tvelliott/SDR_at86rf215/firmware/channel_filter.c

//MIT License
//
//Copyright (c) 2018 tvelliott
//
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




#include <math.h>
#include <float.h>
#include <complex.h>
#include "arm_math.h"
#include "channel_filter.h"


//decimation

static float32_t fir_dec_state_f32_I_8[NSAMPLES + 128 - 1];
static float32_t fir_dec_state_f32_Q_8[NSAMPLES + 128 - 1];
static arm_fir_decimate_instance_f32 Si_dec_8;
static arm_fir_decimate_instance_f32 Sq_dec_8;

static float32_t fir_dec_state_f32_I_32[NSAMPLES + 128 - 1];
static float32_t fir_dec_state_f32_Q_32[NSAMPLES + 128 - 1];
static arm_fir_decimate_instance_f32 Si_dec_32;
static arm_fir_decimate_instance_f32 Sq_dec_32;

static float32_t dc_state_f32_I[NSAMPLES + 134 - 1];
static float32_t dc_state_f32_Q[NSAMPLES + 134 - 1];
static arm_fir_instance_f32 dc_i;
static arm_fir_instance_f32 dc_q;

static float32_t fir_dec_state_f32_i_stage1[NSAMPLES + 128 - 1];
static float32_t fir_dec_state_f32_q_stage1[NSAMPLES + 128 - 1];
static arm_fir_decimate_instance_f32 fir_i_stage1;
static arm_fir_decimate_instance_f32 fir_q_stage1;

static float32_t fir_dec_state_f32_i_stage2[NSAMPLES + 128 - 1];
static float32_t fir_dec_state_f32_q_stage2[NSAMPLES + 128 - 1];
static arm_fir_decimate_instance_f32 fir_i_stage2;
static arm_fir_decimate_instance_f32 fir_q_stage2;

float32_t iout[256];
float32_t qout[256];

float dc_removal_63[] = {
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
    , 0.00000, -0.00636, -0.00368, 0.00345, 0.00525, 0.00000, -0.00466, -0.00271, 0.00256, 0.00392, 0.00000, -0.00350, -0.00205, 0.00194, 0.00298, 0.00000
    , -0.00267, -0.00157, 0.00148, 0.00228, 0.00000, -0.00205, -0.00120, 0.00114, 0.00174, 0.00000, -0.00156, -0.00091, 0.00087, 0.00132, 0.00000, -0.00118
    , -0.00069, 0.00065, 0.00100, 0.00000, -0.00089, -0.00052, 0.00049, 0.00074, -0.00000, -0.00066, -0.00038, 0.00036, 0.00055, 0.00000, -0.00048, -0.00028
    , 0.00026, 0.00039, 0.00000, -0.00034, -0.00020, 0.00018, 0.00028, -0.00000, -0.00024, -0.00014, 0.00013, 0.00019, 0.00000, -0.00016, -0.00009, 0.00009
    , 0.00013, 0.00000, -0.00011, -0.00006, 0.00006, 0.00008, -0.00000, -0.00007, -0.00004, 0.00004, 0.00005, 0.00000, -0.00004, -0.00002, 0.00002, 0.00003
    , 0.00000, -0.00003, -0.00001, 0.00001, 0.00002, -0.00000, -0.00001, -0.00001, 0.00001, 0.00001, 0.00000, -0.00001, -0.00000, 0.00000, 0.00000, 0.00000
    , -0.00000, -0.00000, 0.00000, 0.00000, 0.00000, -0.00000, -0.00000, 0.00000, 0.00000, 0.00000, -0.00000, -0.00000, 0.00000, 0.00000, -0.00000
  };

int8_t init_dc_removal = 0;
int8_t init_fir_dec_8 = 0;
int8_t init_fir_dec_32 = 0;
int8_t init_fir_stage1 = 0;
int8_t init_fir_stage2 = 0;

static float32_t input_i[NSAMPLES];
static float32_t input_q[NSAMPLES];

/////////////////////////////////////////////////////
/////////////////////////////////////////////////////
void cf_fft_shift( float32_t *data, int len )
{
  float32_t tmp[2048];
  int i;
  if( len > 2048 ) len = 2048;

  for( i = 0; i < len / 2; i++ ) {
    tmp[i] = data[i + len / 2];
  }
  for( i = 0; i < len / 2; i++ ) {
    tmp[i + len / 2] = data[i];
  }
  for( i = 0; i < len; i++ ) {
    data[i] = tmp[i];
  }
}
//////////////////////////////////////////////////////////////////////////////////////////////////////
//////////////////////////////////////////////////////////////////////////////////////////////////////
void do_fircomp_dec2_stage1( float complex *in_data )
{
  int i;

  if( !init_fir_stage1 ) {
    arm_fir_decimate_init_f32( &fir_i_stage1, 128, 2, &fir_comp_filter[0], &fir_dec_state_f32_i_stage1[0], 256 );
    arm_fir_decimate_init_f32( &fir_q_stage1, 128, 2, &fir_comp_filter[0], &fir_dec_state_f32_q_stage1[0], 256 );
    init_fir_stage1 = 1;
  }

  for( i = 0; i < 256; i++ ) {
    input_i[i] = ( float32_t ) creal( in_data[i] );
    input_q[i] = ( float32_t ) cimag( in_data[i] );
  }

  arm_fir_decimate_f32( &fir_i_stage1, input_i, iout, 256 );
  arm_fir_decimate_f32( &fir_q_stage1, input_q, qout, 256 );

}
//////////////////////////////////////////////////////////////////////////////////////////////////////
//////////////////////////////////////////////////////////////////////////////////////////////////////
void do_fircomp_dec2_stage2( float complex *in_data )
{
  int i;

  if( !init_fir_stage2 ) {
    arm_fir_decimate_init_f32( &fir_i_stage2, 128, 2, &fir_comp_filter[0], &fir_dec_state_f32_i_stage2[0], 128 );
    arm_fir_decimate_init_f32( &fir_q_stage2, 128, 2, &fir_comp_filter[0], &fir_dec_state_f32_q_stage2[0], 128 );
    init_fir_stage2 = 1;
  }

  for( i = 0; i < 128; i++ ) {
    input_i[i] = ( float32_t ) creal( in_data[i] );
    input_q[i] = ( float32_t ) cimag( in_data[i] );
  }

  arm_fir_decimate_f32( &fir_i_stage2, input_i, iout, 128 );
  arm_fir_decimate_f32( &fir_q_stage2, input_q, qout, 128 );

}

//////////////////////////////////////////////////////////////////////////////////////////////////////
//////////////////////////////////////////////////////////////////////////////////////////////////////
void do_filter_decimate_8( float complex *iqdata )
{

  int i;

  if( !init_fir_dec_8 ) {
    arm_fir_decimate_init_f32( &Si_dec_8, 128, 8, &channel_filter[0], &fir_dec_state_f32_I_8[0], NSAMPLES );
    arm_fir_decimate_init_f32( &Sq_dec_8, 128, 8, &channel_filter[0], &fir_dec_state_f32_Q_8[0], NSAMPLES );
    init_fir_dec_8 = 1;
  }


  //I filtering

  for( i = 0; i < NSAMPLES; i++ ) {
    input_i[i] = ( float32_t ) creal( iqdata[i] );
    input_q[i] = ( float32_t ) cimag( iqdata[i] );
  }
  arm_fir_decimate_f32( &Si_dec_8, input_i, iout, NSAMPLES );
  arm_fir_decimate_f32( &Sq_dec_8, input_q, qout, NSAMPLES );

}
//////////////////////////////////////////////////////////////////////////////////////////////////////
//////////////////////////////////////////////////////////////////////////////////////////////////////
void do_filter_decimate_32( float complex *iqdata )
{

  int i;

  if( !init_fir_dec_32 ) {
    arm_fir_decimate_init_f32( &Si_dec_32, 128, 32, &channel_filter[0], &fir_dec_state_f32_I_32[0], NSAMPLES );
    arm_fir_decimate_init_f32( &Sq_dec_32, 128, 32, &channel_filter[0], &fir_dec_state_f32_Q_32[0], NSAMPLES );
    init_fir_dec_32 = 1;
  }


  //I filtering

  for( i = 0; i < NSAMPLES; i++ ) {
    input_i[i] = ( float32_t ) creal( iqdata[i] );
    input_q[i] = ( float32_t ) cimag( iqdata[i] );
  }
  arm_fir_decimate_f32( &Si_dec_32, input_i, iout, NSAMPLES );
  arm_fir_decimate_f32( &Sq_dec_32, input_q, qout, NSAMPLES );

}
//static float32_t dc_state_f32_I[NSAMPLES + 128 -1];
//static float32_t dc_state_f32_Q[NSAMPLES + 128 -1];
//static arm_fir_dc_instance_f32 dc_i;
//static arm_fir_dc_instance_f32 dc_q;
//////////////////////////////////////////////////////////////////////////////////////////////////////
//////////////////////////////////////////////////////////////////////////////////////////////////////
float dc_removal( float complex *iqdata, float *ioff, float *qoff )
{

  int i;

  if( !init_dc_removal ) {
    arm_fir_init_f32( &dc_i, 63, &dc_removal_63[0], &dc_state_f32_I[0], NSAMPLES );
    arm_fir_init_f32( &dc_q, 63, &dc_removal_63[0], &dc_state_f32_Q[0], NSAMPLES );
    init_dc_removal = 1;
  }


  for( i = 0; i < NSAMPLES; i++ ) {
    input_i[i] = ( float32_t ) creal( iqdata[i] );
    input_q[i] = ( float32_t ) cimag( iqdata[i] );
  }
  arm_fir_f32( &dc_i, input_i, iout, NSAMPLES );
  arm_fir_f32( &dc_q, input_q, qout, NSAMPLES );

  float f1 = 0.0f;
  float f2 = 0.0f;
  for( i = 0; i < NSAMPLES; i++ ) {
    f1 += iout[i];
    f2 += qout[i];
  }
  *ioff = f1;
  *qoff = f2;

}
