tvelliott/SDR_at86rf215/firmware/fpga_image.h

//filename: fpga/src/fpga_top.bin
//input file length: 135100
//compressed len: 31387
const uint8_t rle_compressed_fpga_image[] = {
  0xff, 0x00, 0x00, 0x00, 0xff, 0x7e, 0xaa, 0x99, 0x7e, 0x51, 0x00, 0x01, 0x05, 0x92, 0x00, 0x20, 0x62, 0x03, 0x67, 0x72, 0x01, 0x10, 0x82, 0x00, 0x00, 0x00, 0x11, 0x00, 0x01, 0x01, 0x00, 0x00, 0x00,
  0x15, 0x80, 0x00, 0x00, 0x03, 0x02, 0x00, 0x00, 0x04, 0x08, 0x00, 0x00, 0x17, 0x80, 0x00, 0x00, 0x03, 0x02, 0x00, 0x00, 0x04, 0x08, 0x00, 0x00, 0x04, 0x20, 0x00, 0x00, 0x05, 0x07, 0x00, 0x00,
  0x28, 0x0d, 0x00, 0x00, 0x40, 0x80, 0x00, 0x00, 0x0a, 0xd0, 0x00, 0x00, 0x0b, 0x04, 0x00, 0x00, 0x0b, 0x40, 0x00, 0x00, 0x03, 0x01, 0x00, 0x00, 0x04, 0x04, 0x00, 0x00, 0x17, 0x40, 0x00, 0x00,
  0x03, 0x01, 0x00, 0x00, 0x04, 0x04, 0x00, 0x00, 0x04, 0x10, 0x00, 0x00, 0x11, 0x04, 0x00, 0x00, 0x6e, 0x20, 0x00, 0x00, 0x17, 0x80, 0x00, 0x00, 0x00, 0x03, 0x00, 0x00, 0x00, 0x02, 0x00, 0x00,
  0x01, 0x08, 0x00, 0x00, 0x00, 0x08, 0x00, 0x00, 0x17, 0x80, 0x00, 0x00, 0x00, 0x01, 0x00, 0x00, 0x00, 0x02, 0x00, 0x00, 0x01, 0x04, 0x00, 0x00, 0x00, 0x08, 0x00, 0x00, 0x01, 0x10, 0x00, 0x00,
  0x00, 0x20, 0x00, 0x00, 0x01, 0x40, 0x00, 0x00, 0x20, 0x40, 0x00, 0x00, 0x0b, 0x03, 0x00, 0x00, 0x04, 0x04, 0x00, 0x00, 0x04, 0x30, 0x00, 0x00, 0x16, 0x01, 0x00, 0x00, 0x04, 0x04, 0x00, 0x00,
  0x04, 0x10, 0x00, 0x00, 0x04, 0xc0, 0x00, 0x00, 0x33, 0x14, 0x00, 0x00, 0xc4, 0x10, 0x00, 0x00, 0x18, 0x20, 0x00, 0x00, 0x05, 0xe0, 0x00, 0x00, 0x10, 0x80, 0x00, 0x00, 0x03, 0x10, 0x00, 0x00,
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
  0x04, 0x00, 0x0c, 0xcc, 0x00, 0x20, 0x00, 0x50, 0x00, 0x23, 0x30, 0x00, 0x80, 0x00, 0x00, 0x01, 0x8c, 0xc0, 0x04, 0x00, 0x00, 0x3d, 0x3e, 0x00, 0x00, 0x02, 0x10, 0x00, 0x00, 0x00, 0xa0, 0x04,
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
};
