tvelliott/SDR_at86rf215/firmware/ext_tuner/main.h

/**
  ******************************************************************************
  * @file    main.h
  * @author  MCD Application Team
  * @version V1.0.0
  * @date    19-September-2011
  * @brief   Header for main.c module
  ******************************************************************************
  * @attention
  *
  * THE PRESENT FIRMWARE WHICH IS FOR GUIDANCE ONLY AIMS AT PROVIDING CUSTOMERS
  * WITH CODING INFORMATION REGARDING THEIR PRODUCTS IN ORDER FOR THEM TO SAVE
  * TIME. AS A RESULT, STMICROELECTRONICS SHALL NOT BE HELD LIABLE FOR ANY
  * DIRECT, INDIRECT OR CONSEQUENTIAL DAMAGES WITH RESPECT TO ANY CLAIMS ARISING
  * FROM THE CONTENT OF SUCH FIRMWARE AND/OR THE USE MADE BY CUSTOMERS OF THE
  * CODING INFORMATION CONTAINED HEREIN IN CONNECTION WITH THEIR PRODUCTS.
  *
  * <h2><center>&copy; COPYRIGHT 2011 STMicroelectronics</center></h2>
  ******************************************************************************
  */

/* Define to prevent recursive inclusion -------------------------------------*/
#ifndef __STM32F4_DISCOVERY_DEMO_H
#define __STM32F4_DISCOVERY_DEMO_H

/* Includes ------------------------------------------------------------------*/
#include "stm32f4_discovery.h"
#include <stdio.h>

void TimingDelay_Decrement(void);
void Delay(__IO uint32_t nTime);
void Fail_Handler(void);
#endif /* __STM32F4_DISCOVERY_DEMO_H */

/******************* (C) COPYRIGHT 2011 STMicroelectronics *****END OF FILE****/
