tvelliott/SDR_at86rf215/firmware/ext_tuner/syscalls_newlib.c

//MIT License
//
//Copyright (c) 2018 tvelliott
//
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

#include <sys/types.h>
#include <stdint.h>
#include <errno.h>


extern int32_t _heap;
static unsigned char *heap_ptr = NULL;
int errno;
int _errno;

//calling pow() function causes errors with newlib
//including <errno.h> didn't help
//newlib was complaining about __error not being defined
//no idea if this is right, but compiles
int32_t error = 0;
int * __errno( void )
{
  return &error;
}

//////////////////////////////////////////////////////////////
//  this is used by libc (newlib) when calling malloc / free
//  the heap area is defined in main.ld
//////////////////////////////////////////////////////////////
caddr_t _sbrk(int32_t incr)
{
  unsigned char *prev_heap;

  if(heap_ptr == NULL) {
    heap_ptr = (unsigned char *)&_heap;
  }

  prev_heap = heap_ptr;
  heap_ptr += incr;

  return (caddr_t) prev_heap;
}

//    sbrk
//    Increase program data space.
//    As malloc and related functions depend on this, it is useful to have a working implementation.
//
//    The following suffices for a standalone system;
//    it exploits the symbol end automatically defined by the GNU linker.
//
//    caddr_t sbrk(int incr){
//      extern char end;    /* Defined by the linker */
//      static char *heap_end;
//      char *prev_heap_end;
//
//      if (heap_end == 0) {
//        heap_end = &end;
//      }
//     prev_heap_end = heap_end;
//      if (heap_end + incr > &_stack)
//        {
//          _write (1, "Heap and stack collision\n", 25);
//          abort ();
//        }
//
//      heap_end += incr;
//      return (caddr_t) prev_heap_end;
//    }


int _close(int file)
{
  return -1;
}

char *__env[1] = { 0 };
char **environ = __env;

#include <errno.h>
#undef errno
extern int errno;
int _execve(char *name, char **argv, char **env)
{
  errno=ENOMEM;
  return -1;
}

#include <errno.h>
#undef errno
extern int errno;
int _fork()
{
  errno=EAGAIN;
  return -1;
}

#include <sys/stat.h>
int _fstat(int file, struct stat *st)
{
  st->st_mode = S_IFCHR;
  return 0;
}

int _getpid()
{
  return 1;
}

int _isatty(int file)
{
  return 1;
}

#include <errno.h>
#undef errno
extern int errno;
int _kill(int pid, int sig)
{
  errno=EINVAL;
  return(-1);
}

#include <errno.h>
#undef errno
extern int errno;
int _link(char *old, char *new)
{
  errno=EMLINK;
  return -1;
}

void _exit(int status)
{
}

int _lseek(int file, int ptr, int dir)
{
  return 0;
}

int _open(const char *name, int flags, int mode)
{
  return -1;
}

int _read(int file, char *ptr, int len)
{
  return 0;
}


int _stat(const char *file, struct stat *st)
{
  st->st_mode = S_IFCHR;
  return 0;
}

clock_t _times(struct tms *buf)
{
  return -1;
}

#include <errno.h>
#undef errno
extern int errno;
int _unlink(char *name)
{
  errno=ENOENT;
  return -1;
}

#include <errno.h>
#undef errno
extern int errno;
int _wait(int *status)
{
  errno=ECHILD;
  return -1;
}

int _write(int file, char *ptr, int len)
{
  //int todo;

  //for (todo = 0; todo < len; todo++) {
  //   writechar(*ptr++);
  //}
  //return len;
  return 0;
}

void abort()
{
  //while(1);//don't know, force wdt
}
