tvelliott/SDR_at86rf215/firmware/fpga/src/ddr_in.v

//MIT License
//
//Copyright (c) 2018 tvelliott
//
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



//////////////////////////////////////////////////
//author t.elliott 2018
//DDR I/Q data receiver for use with AT86RF215
//
// rising edge of data_valid should be used to latch data_i and data_q
//

module ddr_in (
    input clk,
    input data_in,
    input rst_ddr,
    output wire [12:0] data_i, 
    output wire [12:0] data_q,
    output reg sync,
    output reg data_valid
);

reg qa_q;
reg qb_q;
reg sync;
reg dv;

reg [31:0] data_reg;
reg [3:0] sync_cnt;
reg [3:0] sync_to;

always @(negedge clk) begin
    qb_q <= data_in;  //Q data on falling edge
end

always @(posedge clk) begin

    if (rst_ddr) begin
      data_reg <= 32'b0;
      data_i <= 13'b0;
      data_q <= 13'b0;
      sync <= 1'b0;
      dv <= 1'b0;
      data_valid <= 1'b0;
    end 
    else 
    begin

      qa_q <= data_in;  //I data on rising edge

      data_reg <= { data_reg[29:0], qa_q, qb_q }; //shift in 2 bits every rising edge

      sync_cnt <= sync_cnt+1;

      if(!sync) 
      begin
        //initial sync check to reset sync_cnt clock
        if(data_reg[31:30]==2'b10 && data_reg[16]==1'b0 && data_reg[15:14]==2'b01 && data_reg[0]==1'b0) //sync bit pattern for AT86RF215
        begin  
          sync_cnt <= 4'h1;
          sync <= 1'b1;
          sync_to <= 4'hb;
        end
      end 
      else 
      begin 

        if(sync_cnt==4'h0) 
        begin
          if(data_reg[31:30]==2'b10 && data_reg[16]==1'b0 && data_reg[15:14]==2'b01 && data_reg[0]==1'b0) //sync bit pattern for AT86RF215
          begin  
            sync_to <= 4'hb;  //we are still synced, so reset the timeout counter
            dv<=1'b1;
          end 
          else 
          begin
            if(sync_to!=4'h0) 
              sync_to <= sync_to-1;
            else 
              sync <= 1'b0; //lost sync
          end
        end

      end

      if(sync_cnt[3]==1'b1) 
          dv<=1'b0;

      //generate a data_valid signal with frequency of Fs (400Khz - 4Mhz). data_valid rising edge is centered on the I/Q data words
      if(dv && sync_cnt[3]==1'b0) 
      begin
        data_i[12:0] <= data_reg[29:17];
        data_q[12:0] <= data_reg[13:1];
        data_valid <= 1'b1;
      end 
      else 
        data_valid <= 1'b0;
    end
end

endmodule
